westonb/Plasma-Driver/simulation/class_E_final.asc

C1: cap; 37p
C2: cap; 0.1µ
C3: cap; 20p
C4: cap; 246p
C5: cap; 129p
L1: ind; 120n; Rser=0.5
L2: ind; 1.2µ
L3: ind; 82n; Rser=0.5
L4: ind; 200n
M4: nmos; MRF101AN
R1: res; 750
R2: res; 1
R3: res; 50
V1: voltage; PULSE(0 4.5 0 0.5n 0.5n {0.5*PERIOD} {PERIOD})
V2: voltage; 32
V3: voltage; 2
Named nets: 0, VIN, VGS
.param FREQ=40.68E6
.param PERIOD 1/{FREQ}
.tran 0 {1000*PERIOD} {996*PERIOD}
.model MRF101AN VDMOS(Rg=4 Rd=1 Rs=0.1 Vto=2.2 Kp=7.1 Lambda=0 mtriode=0.692 subthres=1.07m Cgdmax=5p Cgdmin=1p Cgs=130p Cjo=130p M=0.4 Vj=2.3 BV=140 tt=1n)
.meas Pin AVG -V(vin)*I(V2)
.meas Vmax MAX V(Vds)
.meas Pout AVG V(Vout)*I(R2)
.meas Ploss AVG V(Vds)*Id(M4)+V(Vgs)*Ig(M4)
.param Rl 100
.param Cl 391p
.param Ll 234n
